cracked-machine/BassStationSequencerMidiController/SequencerMidiController/Docs/3d/89f2962_221790-1.stp

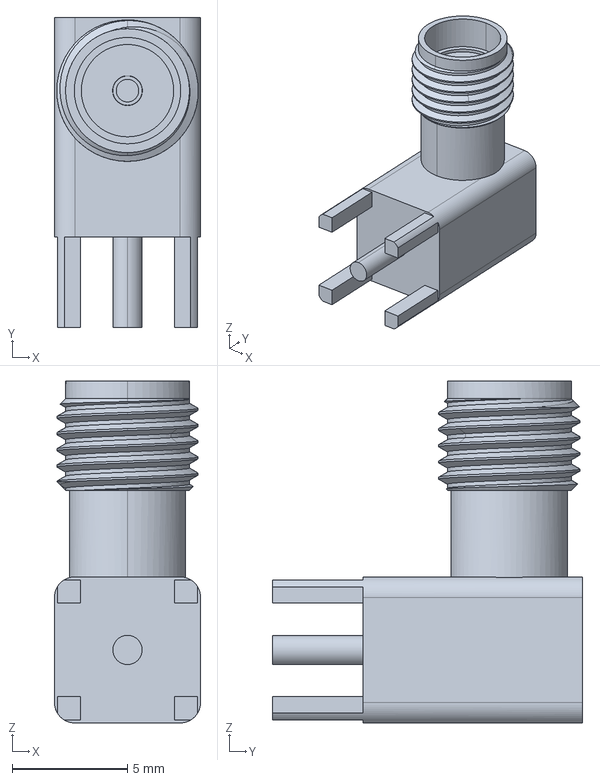
[picture p18: CAD file, 2021-06-07]
SequencerMidiController/Docs/3d/89f2962_221790-1.stp
6.35 x 13.5 x 14.9 mm
