cracked-machine/BassStationSequencerMidiController/SequencerMidiController/Docs/3d/User Library-Eagle Plastic Devices 45KN018-GRX.STEP

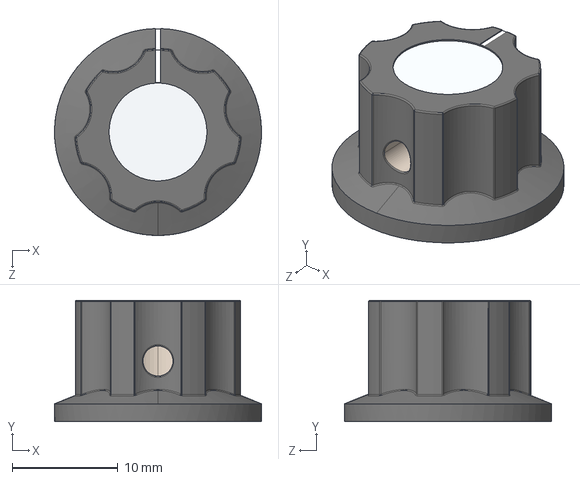
[picture p19: CAD file, 2021-06-07]
SequencerMidiController/Docs/3d/User Library-Eagle Plastic Devices 45KN018-GRX.STEP
19.6 x 11.5 x 19.6 mm
