cracked-machine/BassStationSequencerMidiController/SequencerMidiController/Docs/3d/s2751-46r.stp

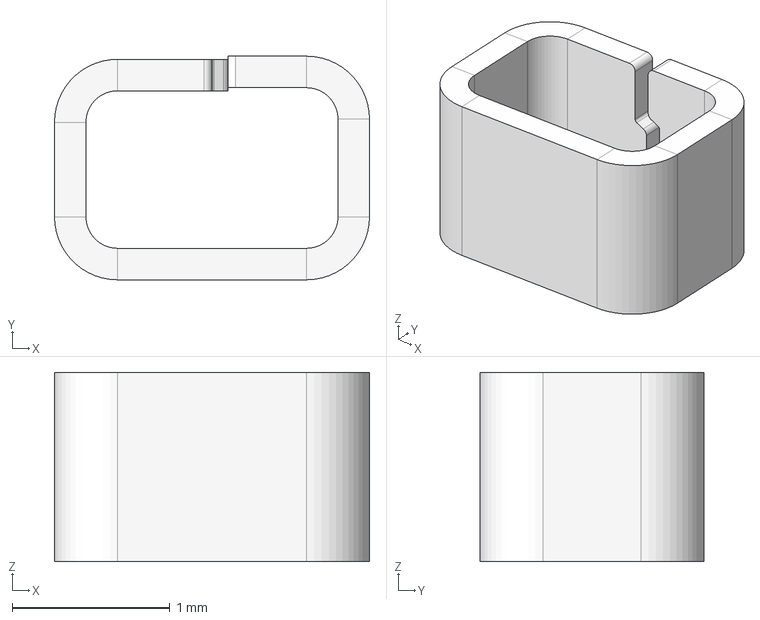
[picture p20: CAD file, 2021-06-07]
SequencerMidiController/Docs/3d/s2751-46r.stp
2.00 x 1.42 x 1.20 mm
